wahlencraft/pico-alarm-clock/images/circuit/circuit.sch

## KiCad design images/circuit/circuit.sch (2021-07-09)

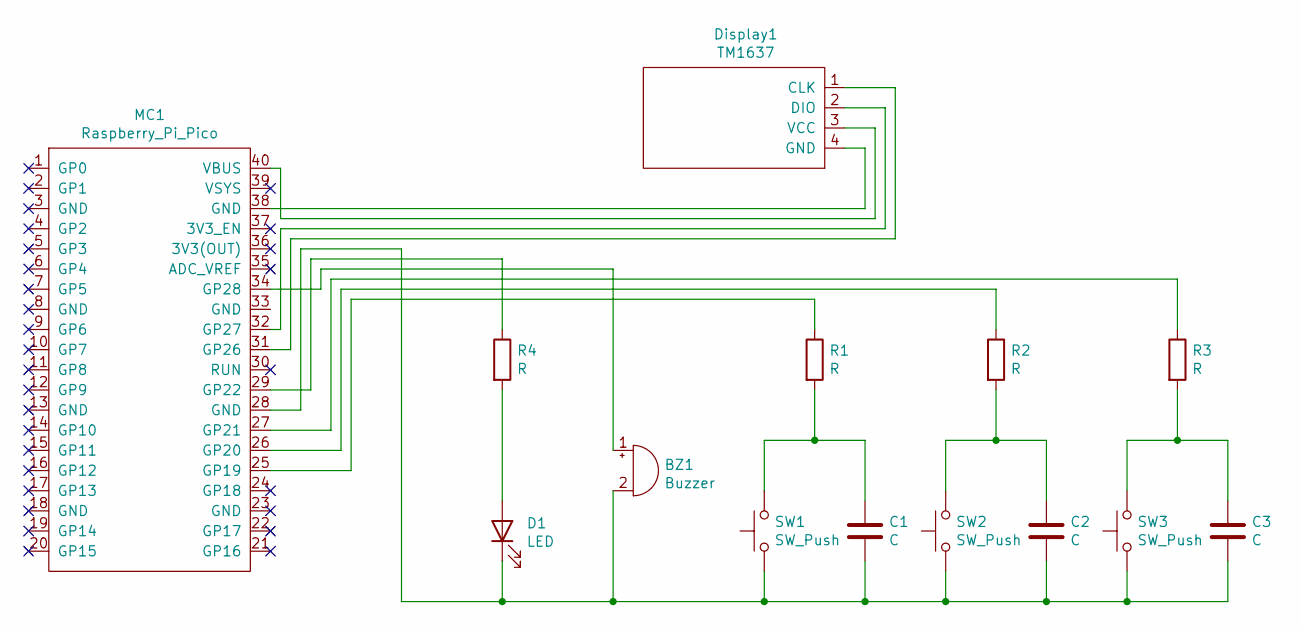
[picture p5: schematic circuit.sch]

Parts:
BZ1: Buzzer
C1, C2, C3: C
D1: LED
Display1: TM1637
MC1: Raspberry_Pi_Pico
R1, R2, R3, R4: R
SW1, SW2, SW3: SW_Push

Connections:
unnamed: BZ1.1 (-), MC1.34 (GP28)
unnamed: BZ1.2 (+), C1.2, C2.2, C3.2, D1.1 (K), MC1.28 (GND), SW1.2, SW2.2, SW3.2
unnamed: C1.1, R1.2, SW1.1
unnamed: C2.1, R2.2, SW2.1
unnamed: C3.1, R3.2, SW3.1
unnamed: D1.2 (A), R4.2
unnamed: Display1.1 (CLK), MC1.31 (GP26)
unnamed: Display1.2 (DIO), MC1.32 (GP27)
unnamed: Display1.3 (VCC), MC1.40 (VBUS)
unnamed: Display1.4 (GND), MC1.38 (GND)
unnamed: MC1.25 (GP19), R1.1
unnamed: MC1.26 (GP20), R2.1
unnamed: MC1.27 (GP21), R3.1
unnamed: MC1.29 (GP22), R4.1
