wahlencraft/pico-alarm-clock/src/alarm.h

/** 
 * alarm.h
 * 
 * Start, maintain and stop the alarm.
 *
 * - Alarm: A time based event stored as a node.
 * - Song: The sound associated with the alarm.
**/

#ifndef ALARM_H_
#define ALARM_H_

#include <stdio.h>
#include <stdbool.h>
#include <stdlib.h>
#include <inttypes.h>

#include <pico/stdlib.h>
#include <hardware/clocks.h>
#include <hardware/pwm.h>
#include <PicoTM1637.h>

#include <song_def.h>
#include <pins.h>
#include <node.h>

void init_alarms();

int get_number_of_songs();

/* Start a new song with song 'songNum'. */
void start_song(int songNum);

/* Turn of the running song. */
void stop_song();

/* Update state in the running song. 
 *
 * Returns the time in ms for when it shuld be run again. Warning, if not run
 * at thease intervals, sound might glich out. */
int64_t update_running_song();

/* Turn of led. */
void led_clear();

/* Add a new alarm.
 *
 * The alarm will be put in a list of alarm sorted after the time of the alarm.
 * Returns EXIT_FAILURE if there already is an alarm at this time.
 *
 * - @param *time: The datetime for when the alarm should fire. Only dotw,
 *   hour, min and sec are important.
 * - @param song: The song that should be played when the alarm fires. The
 *   argument is an index in the songList array defined in `init_alarms`. 
 * - @param active: If the alarm is activated of not. */
int add_alarm(datetime_t *time, int song, bool active);

/* Light led if alarm is active, otherwise turn it off. */
void show_if_alarm_active(node_t *alarm);

inline void toggle_alarm_active(node_t *alarm) {
  alarm->active = !alarm->active;
  DEBUG_PRINT(("Alarm is now %d\n", alarm->active));
}

/* True if there is alarms. */
bool is_alarms();

/* Get the next. Function remembers if it has been called before.
 *
 * - @param alarm: Pointer where the alarm will be returned.
 * - @param restart: If true the list will restart, and the first time will be
 *   used. Otherwise the next time (compared to last call) will be given.
 *   Should always be true on the first call.
 *
 * Exit failure if no next node is found. */
int get_next_alarm(node_t *alarm, bool restart);

/* Check if there is an alarm before next minute. Get that alarm.
 *
 * Returns true if *current time* < *next alarm* <= *next minute*.
 * If true @parmam returnNode will point to said alarm.*/
bool is_alarm_in_1_min(node_t *returnNode);

void print_all_alarms();

/* Remove the alarm at @param time. Get a copy (if not NULL)*/
void remove_alarm(datetime_t *time, node_t *copy);

#endif //ALARM_H_
